blackjetrock/pps4-trace/photos/P1110587.JPG

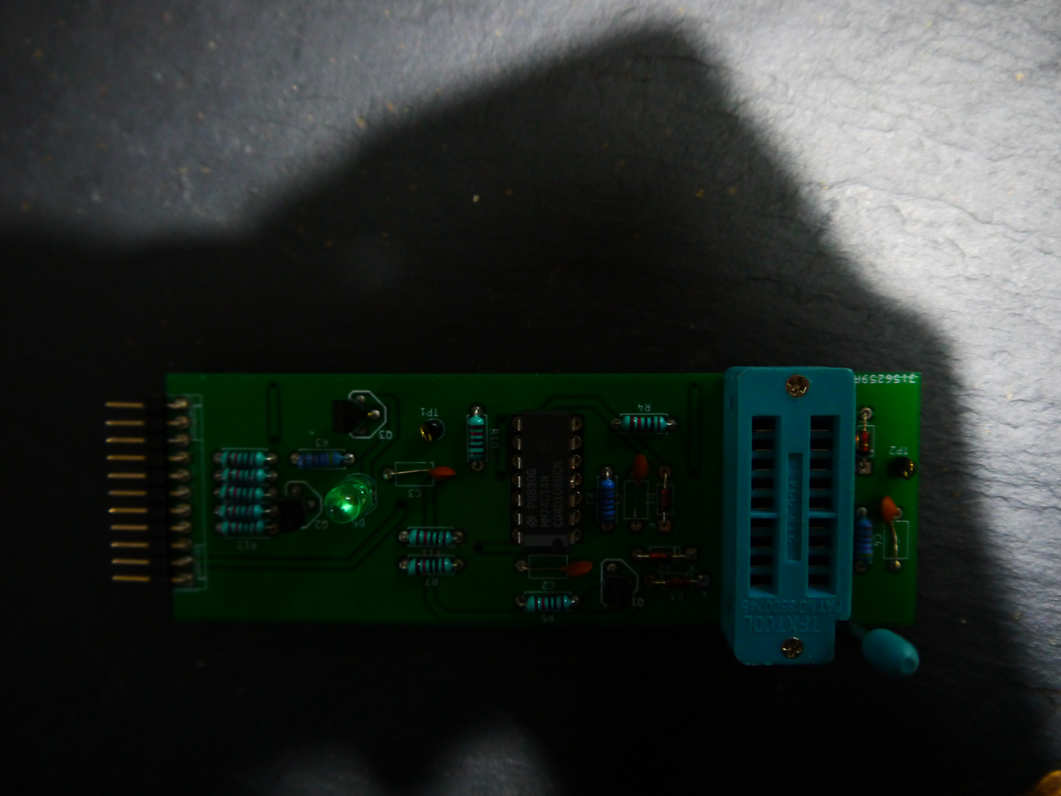
photos/P1110587.JPG
