blackjetrock/pps4-trace/photos/P1110590.JPG

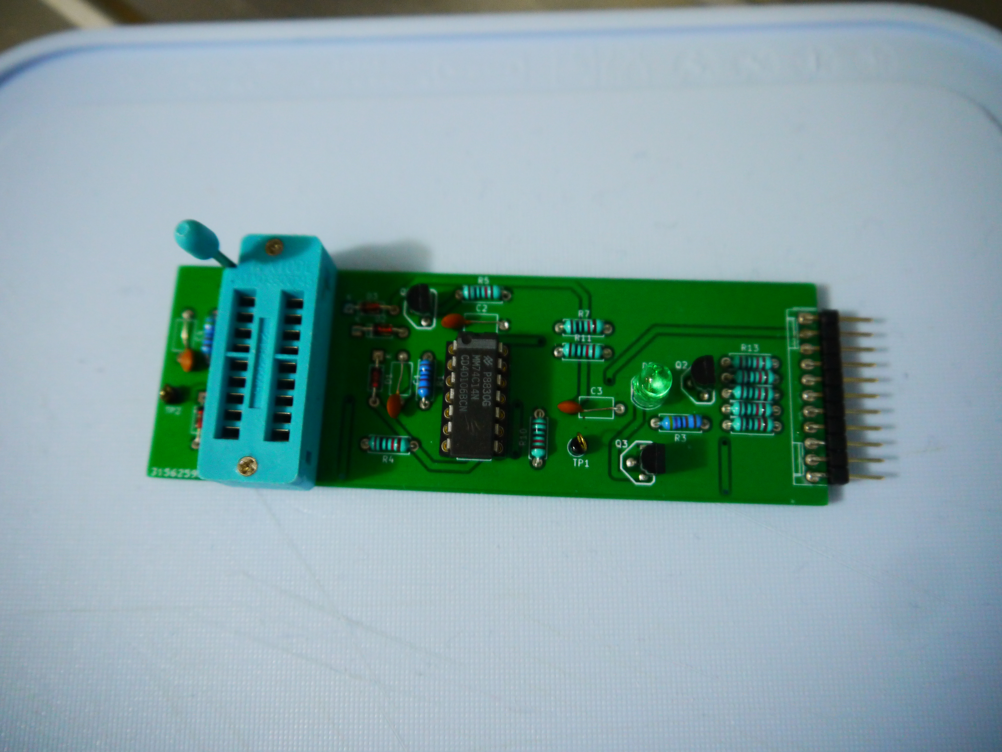
photos/P1110590.JPG
