blackjetrock/pps4-trace/rom-dumper/pictures/IMAG3600.jpg

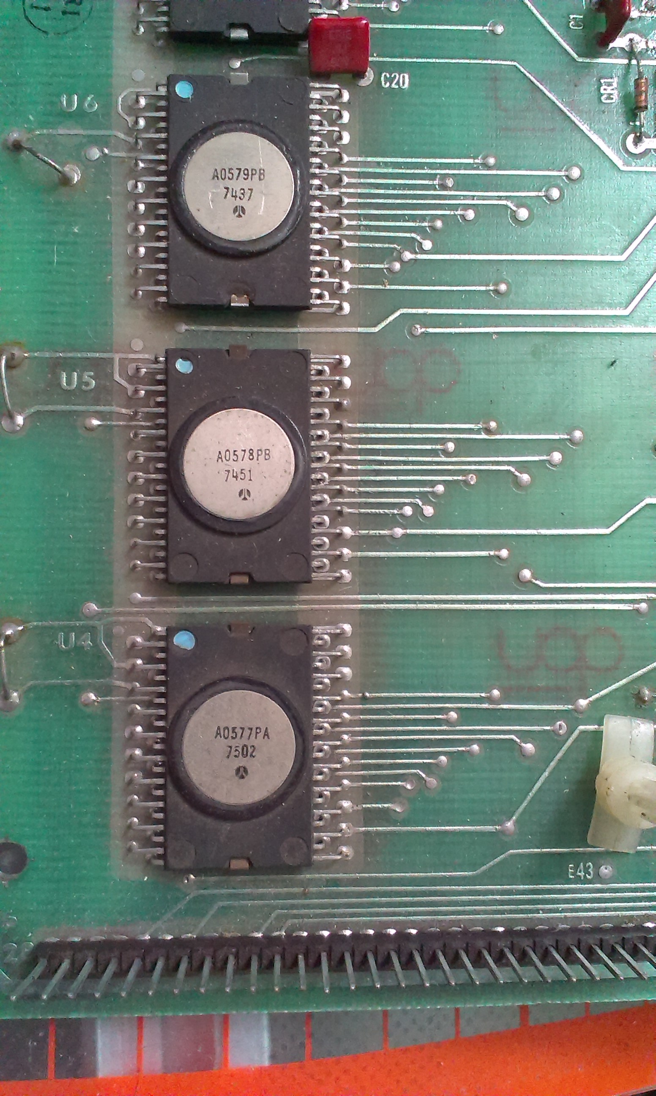
rom-dumper/pictures/IMAG3600.jpg
