blackjetrock/pps4-trace/rom-dumper/pictures/IMAG3601.jpg

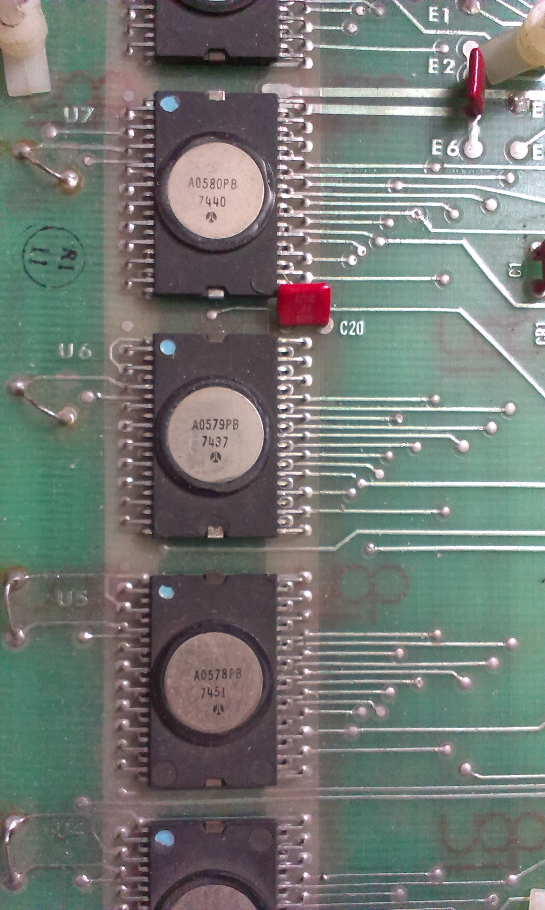
rom-dumper/pictures/IMAG3601.jpg
