blackjetrock/pps4-trace/rom-dumper/pictures/IMAG3602.jpg

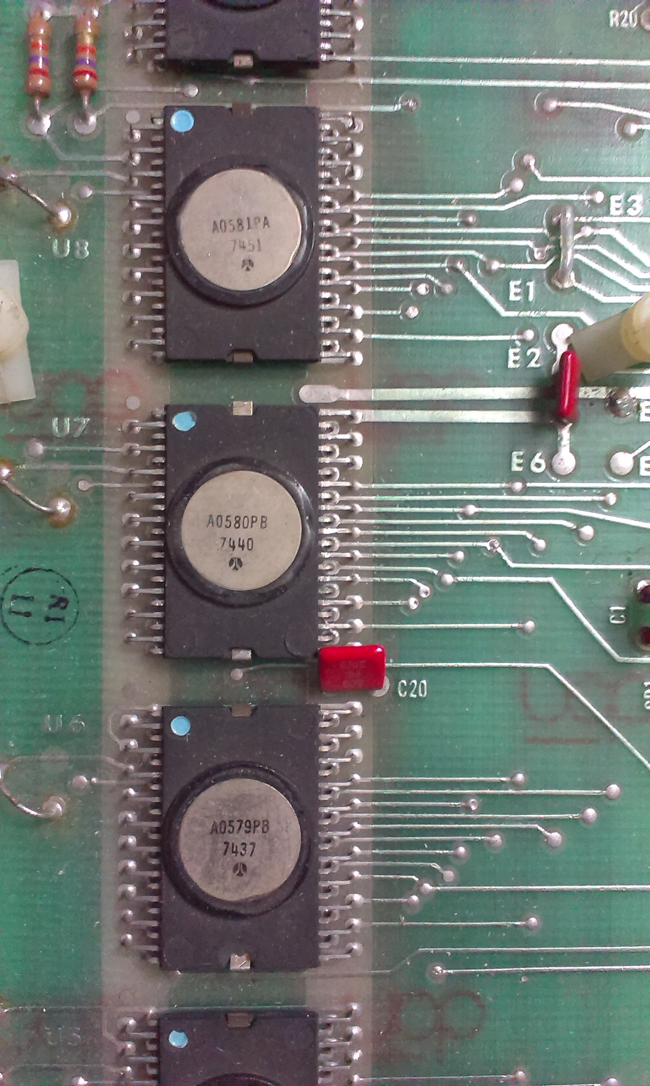
rom-dumper/pictures/IMAG3602.jpg
