blackjetrock/pps4-trace/rom-dumper/pictures/IMAG3603.jpg

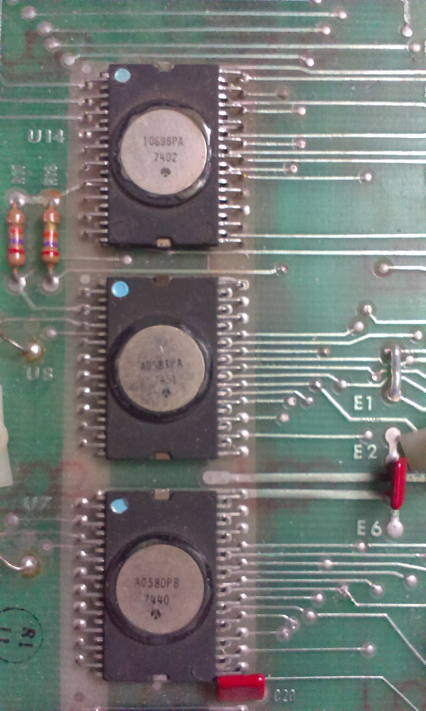
rom-dumper/pictures/IMAG3603.jpg
