blackjetrock/pps4-trace/rom-dumper/pictures/IMAG3604.jpg

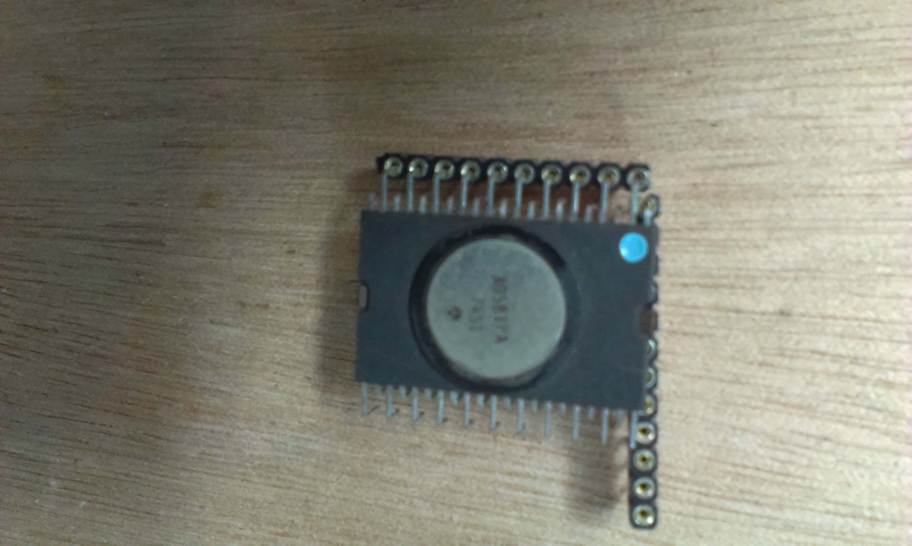
rom-dumper/pictures/IMAG3604.jpg
