blackjetrock/pps4-trace/rom-dumper/pictures/IMAG3605.jpg

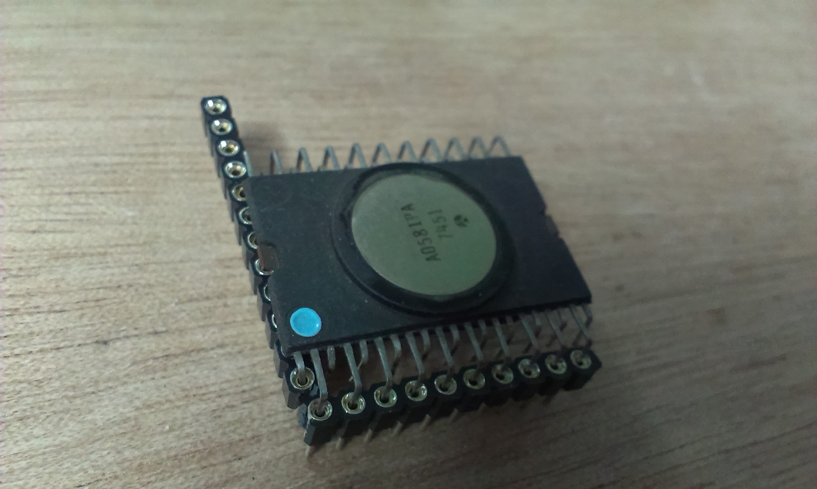
rom-dumper/pictures/IMAG3605.jpg
