blackjetrock/pps4-trace/rom-dumper/pictures/IMAG3606.jpg

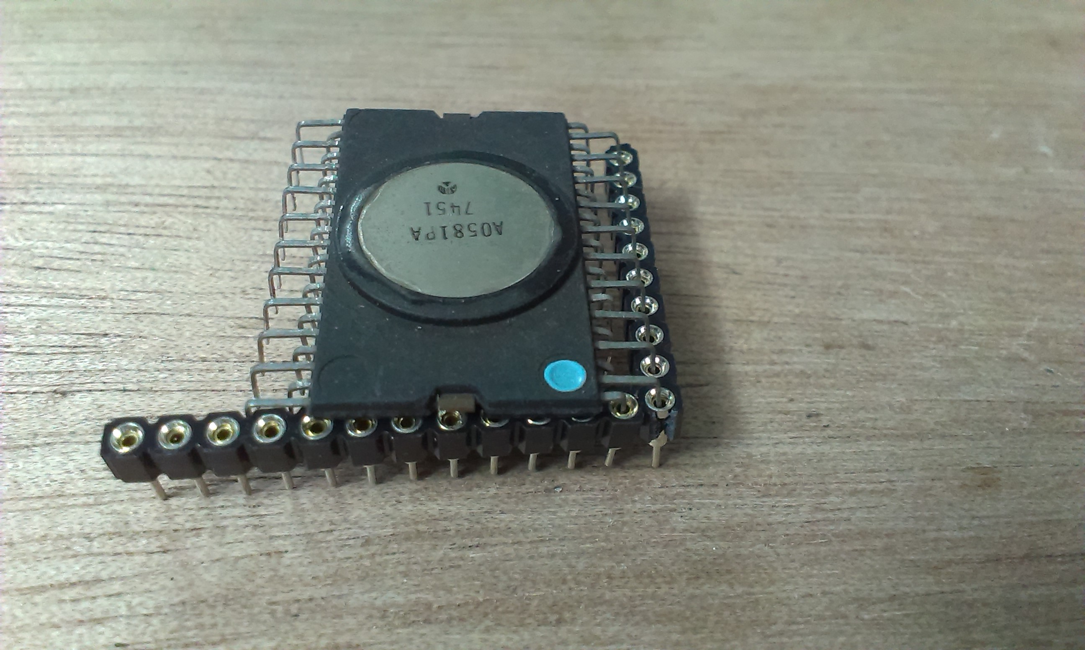
rom-dumper/pictures/IMAG3606.jpg
