blackjetrock/pps4-trace/rom-dumper/pictures/IMAG3607.jpg

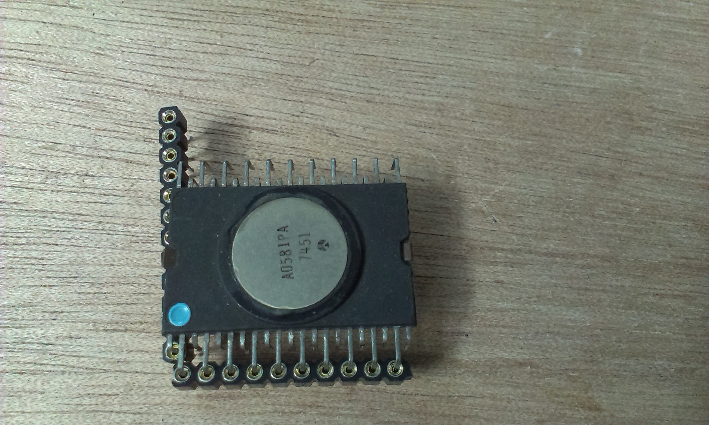
rom-dumper/pictures/IMAG3607.jpg
