blackjetrock/pps4-trace/schematics/IMAG7071.jpg

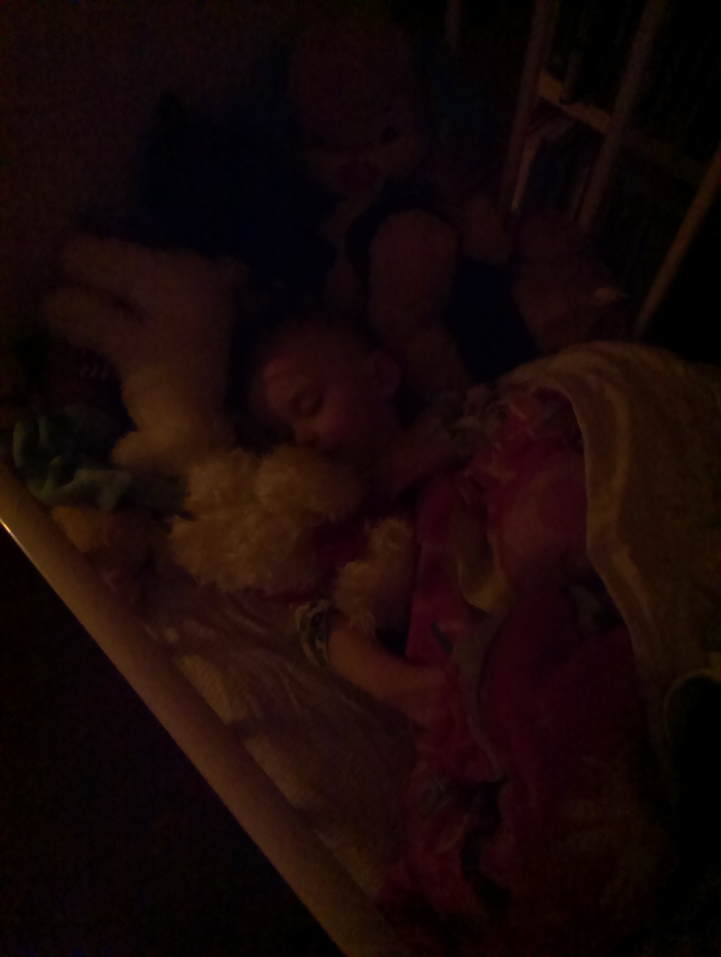
schematics/IMAG7071.jpg
