blackjetrock/pps4-trace/schematics/IMAG7072.jpg

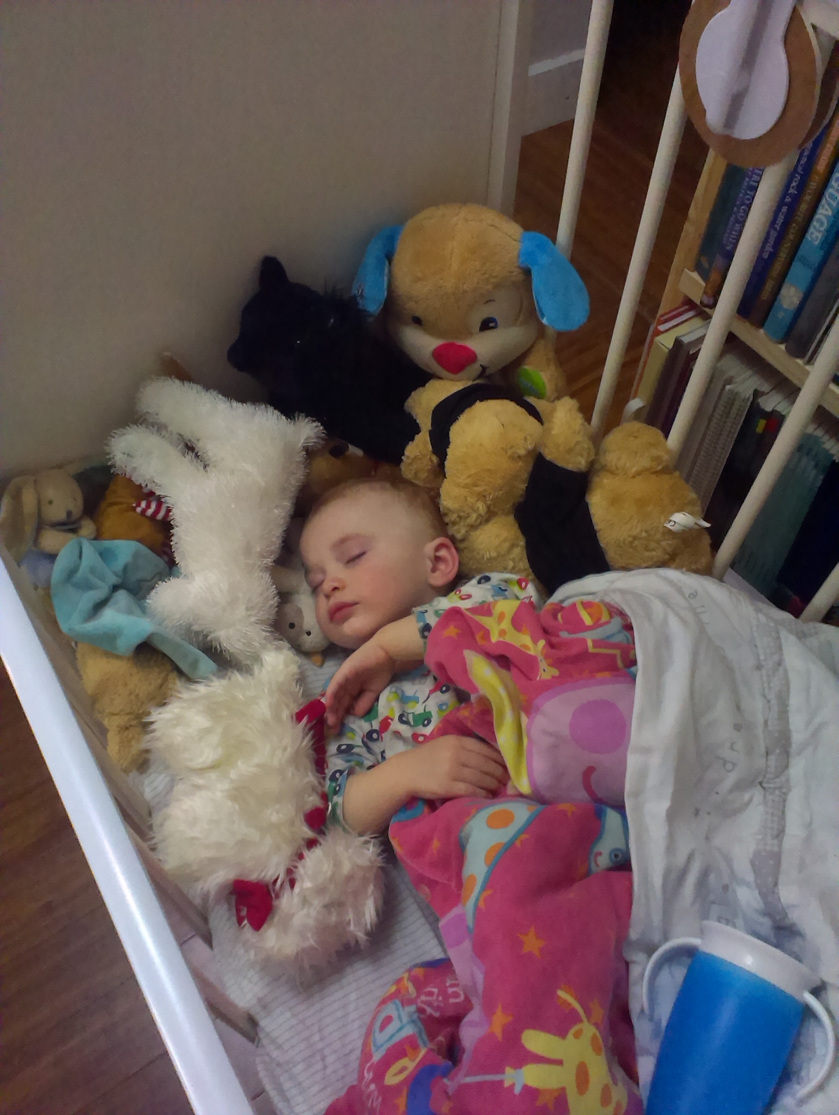
schematics/IMAG7072.jpg
