blackjetrock/pps4-trace/schematics/IMAG7073.jpg

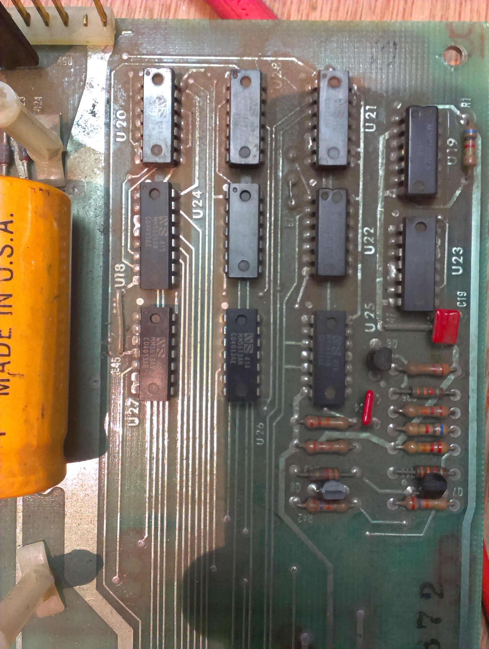
schematics/IMAG7073.jpg
