blackjetrock/pps4-trace/schematics/IMAG7075.jpg

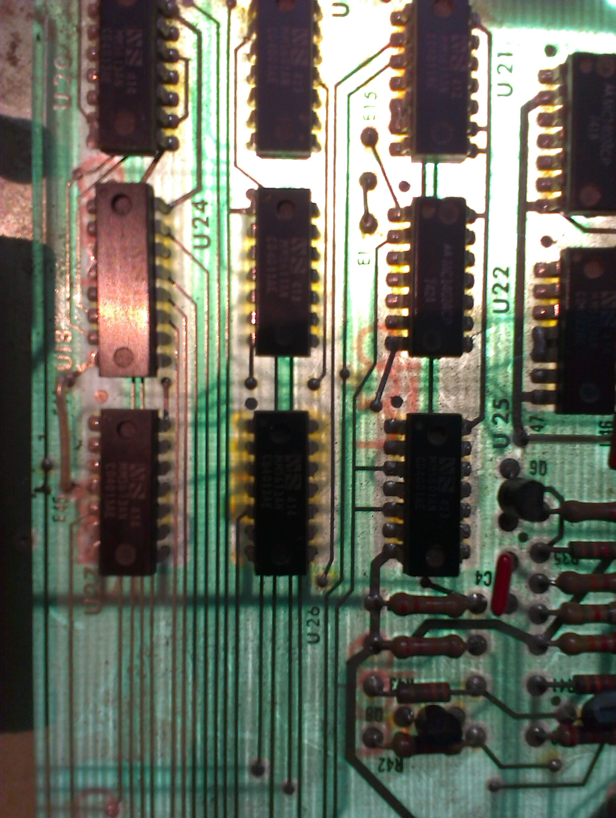
schematics/IMAG7075.jpg
