blackjetrock/pps4-trace/schematics/IMAG7076.jpg

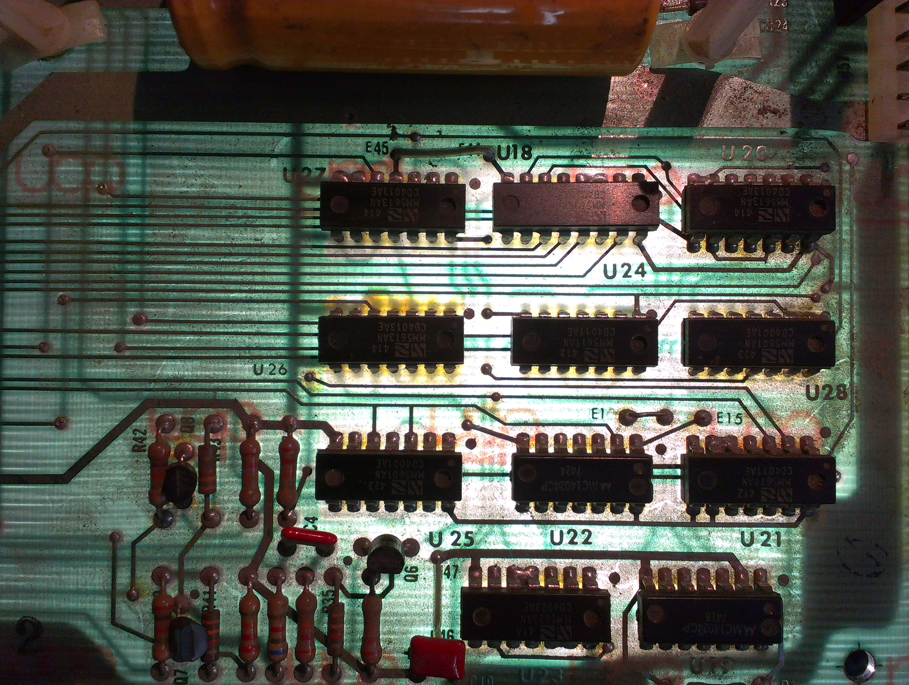
schematics/IMAG7076.jpg
