blackjetrock/pps4-trace/schematics/IMAG7077.jpg

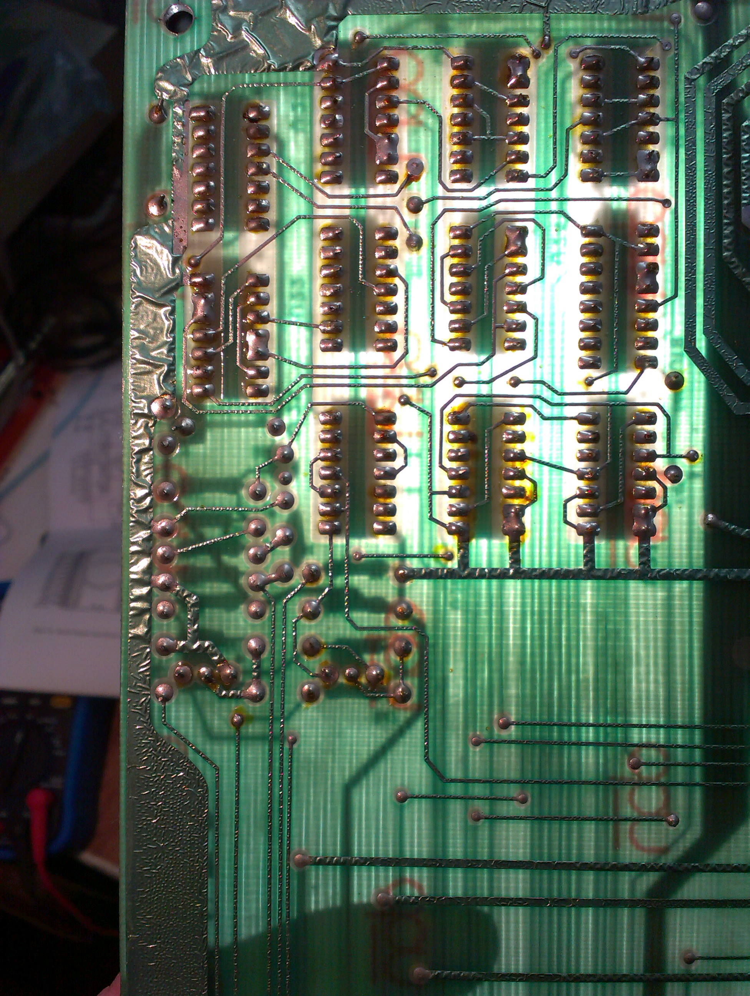
schematics/IMAG7077.jpg
