blackjetrock/pps4-trace/schematics/IMAG7079.jpg

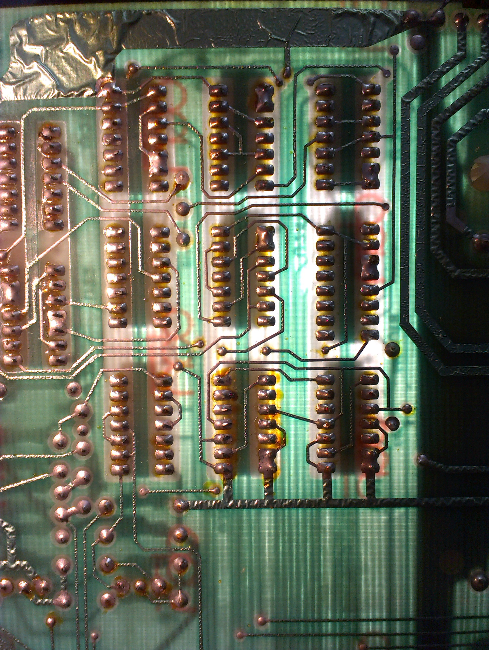
schematics/IMAG7079.jpg
