blackjetrock/pps4-trace/schematics/IMAG7081.jpg

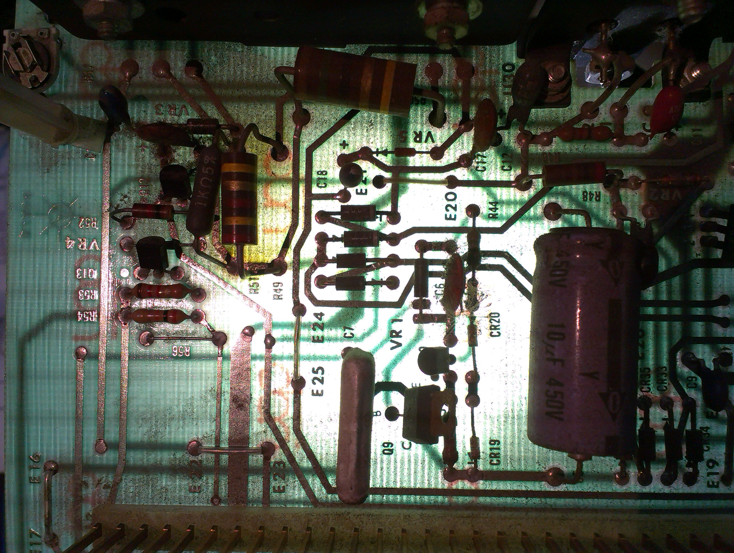
schematics/IMAG7081.jpg
