blackjetrock/pps4-trace/schematics/IMAG7082.jpg

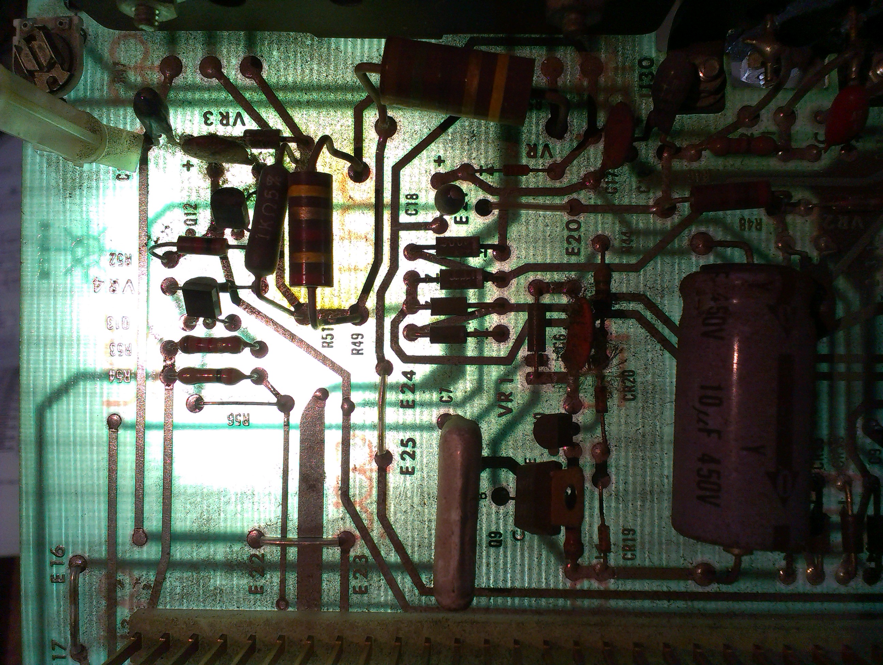
schematics/IMAG7082.jpg
