blackjetrock/pps4-trace/schematics/IMAG7083.jpg

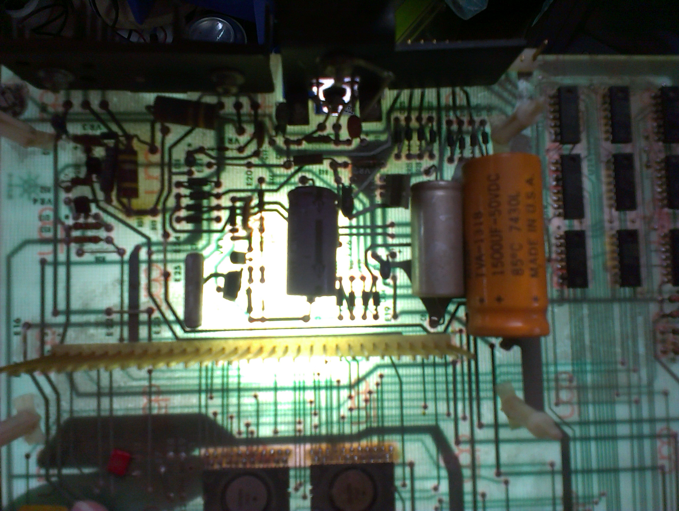
schematics/IMAG7083.jpg
