blackjetrock/pps4-trace/schematics/IMAG7085.jpg

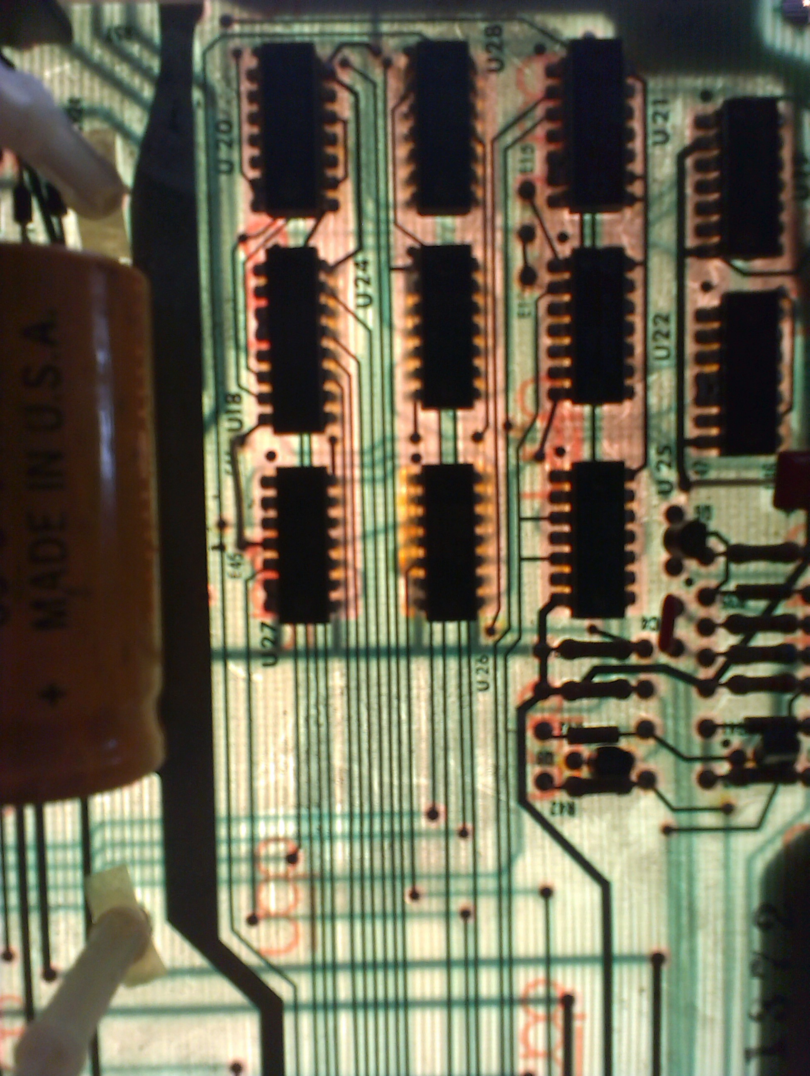
schematics/IMAG7085.jpg
