blackjetrock/pps4-trace/schematics/IMAG7087.jpg

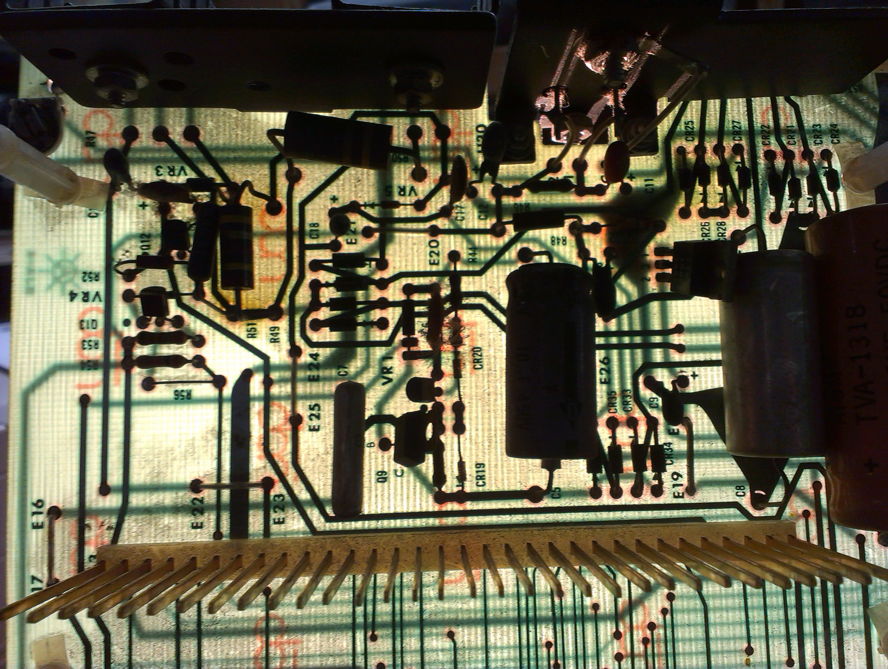
schematics/IMAG7087.jpg
