blackjetrock/pps4-trace/schematics/IMAG7088.jpg

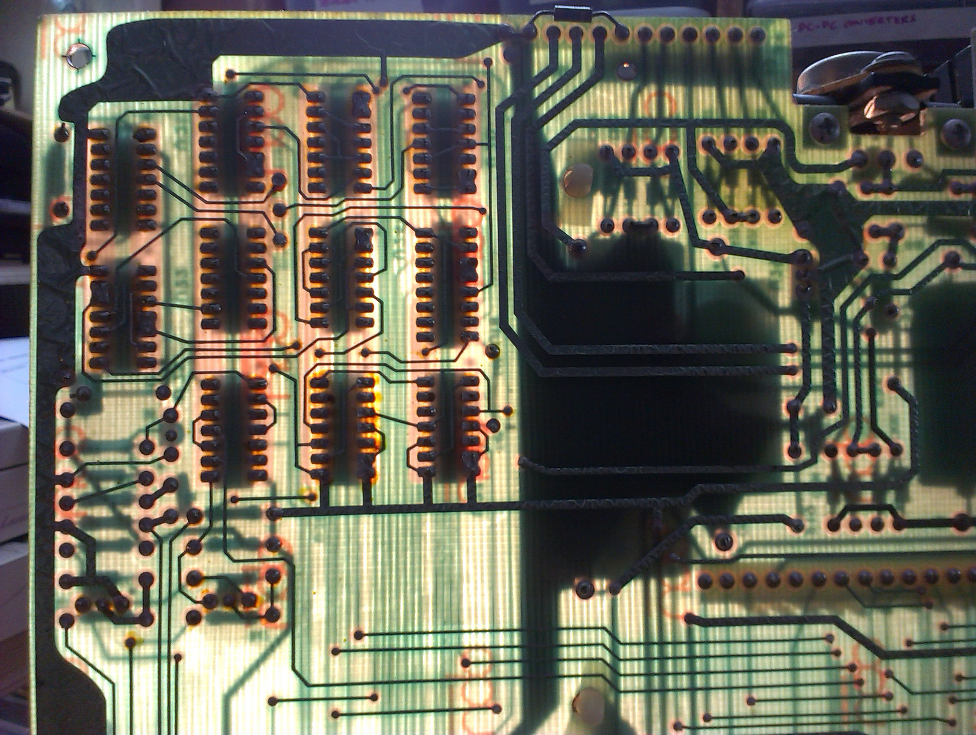
schematics/IMAG7088.jpg
