blackjetrock/pps4-trace/schematics/IMAG7089.jpg

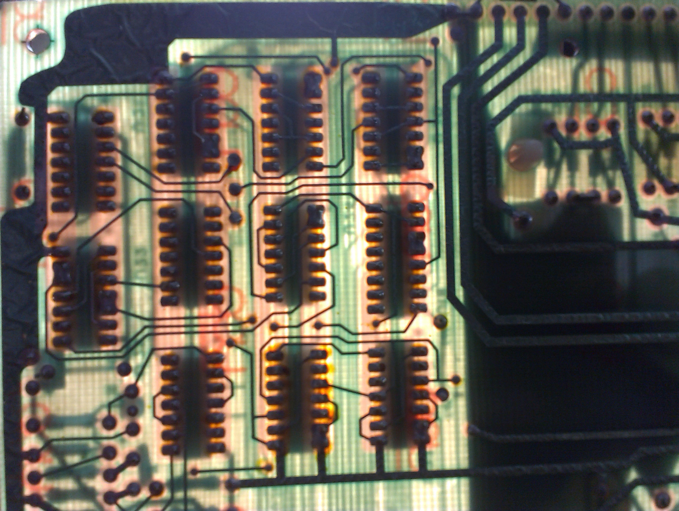
schematics/IMAG7089.jpg
