blackjetrock/pps4-trace/schematics/rockwell920/rockwell920.sch

## KiCad design schematics/rockwell920/rockwell920.sch (2023-04-06)

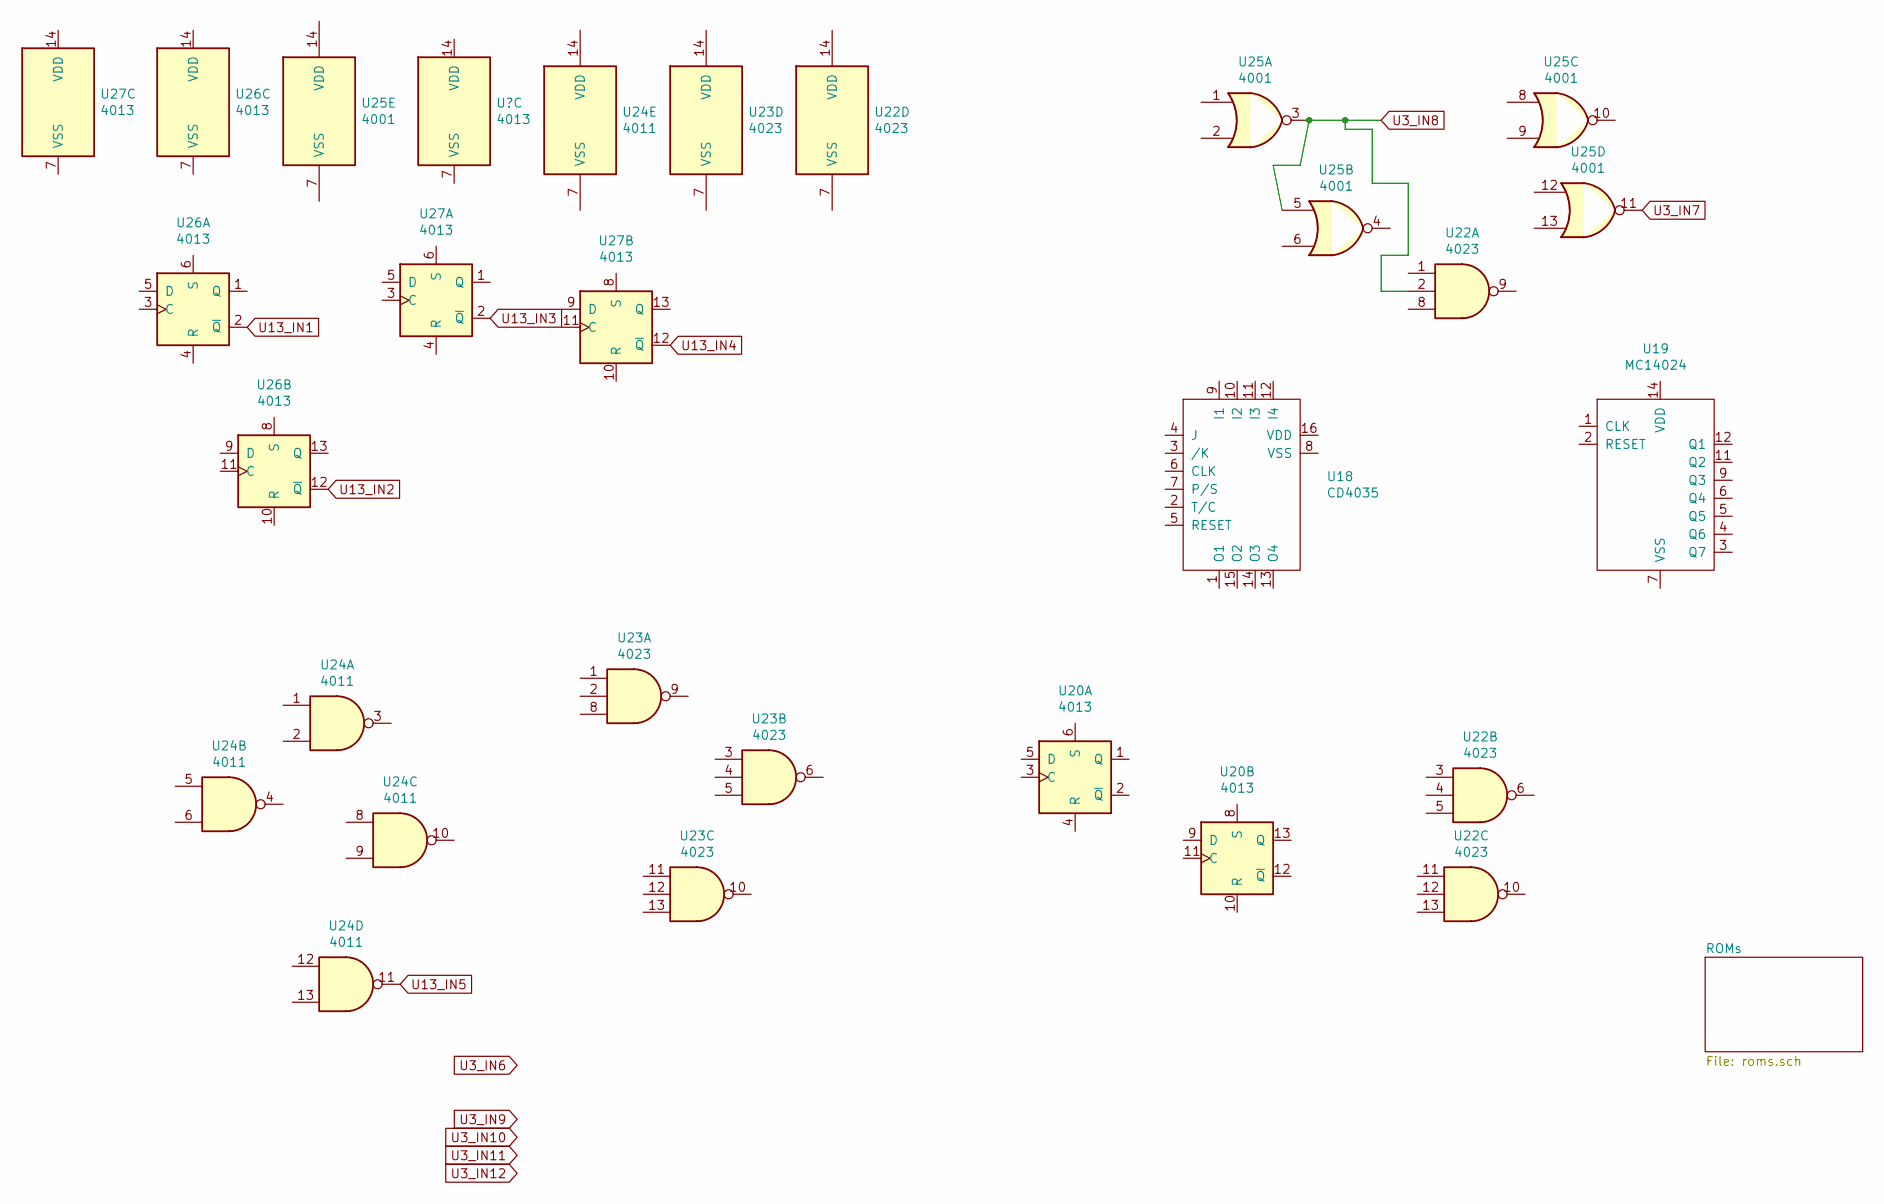
[picture p38: schematic rockwell920.sch]

Parts:
U18: CD4035
U19: MC14024
U20, U26, U27: 4013
U22, U23: 4023
U24: 4011
U25: 4001

Connections:
U3_IN7: U25.11
U3_IN8: U22.2, U25.3, U25.5
U13_IN1: U26.2 (~Q)
U13_IN2: U26.12 (~Q)
U13_IN3: U27.2 (~Q)
U13_IN4: U27.12 (~Q)
U13_IN5: U24.11
