blackjetrock/pps4-trace/schematics/rockwell920/roms.sch

## KiCad design schematics/rockwell920/roms.sch (2023-04-06)

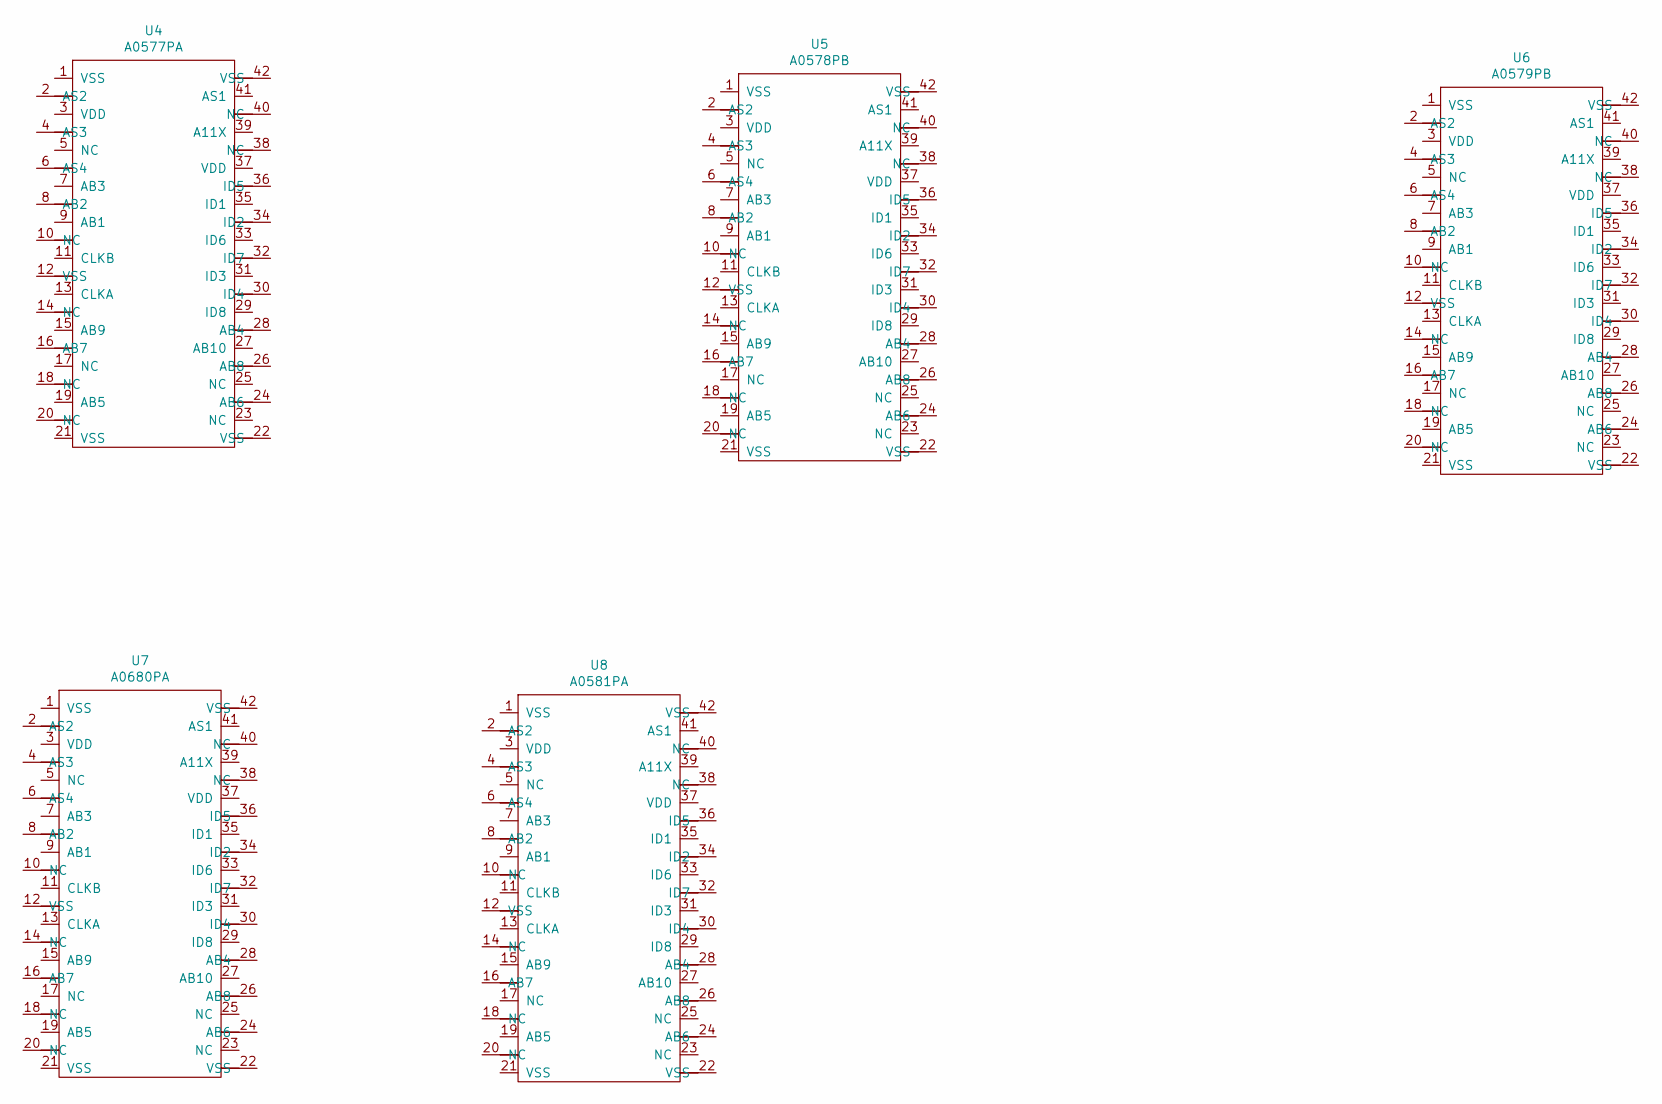
[picture p39: schematic roms.sch]

Parts:
U4: A0577PA
U5: A0578PB
U6: A0579PB
U7: A0680PA
U8: A0581PA
